namachan10777/4x6t2/3dparts/under_spacer.scad

difference() {
	height=5.2+0.5-1.5-1-1.6;
	$fs=0.1;
	cylinder(r=3, h=height);
	cylinder(r=1.75, h=height);
}
